axlan/pcb-map/firmware/simulation/data/map_board_preview.png

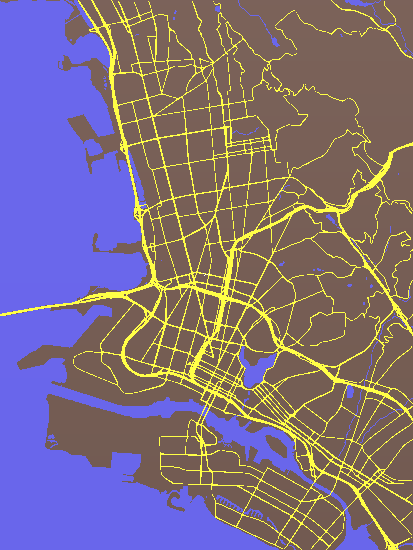
firmware/simulation/data/map_board_preview.png
